FeruzTopalov/spoke/Enclosure/Enterprise/Enterprise_4.jpg

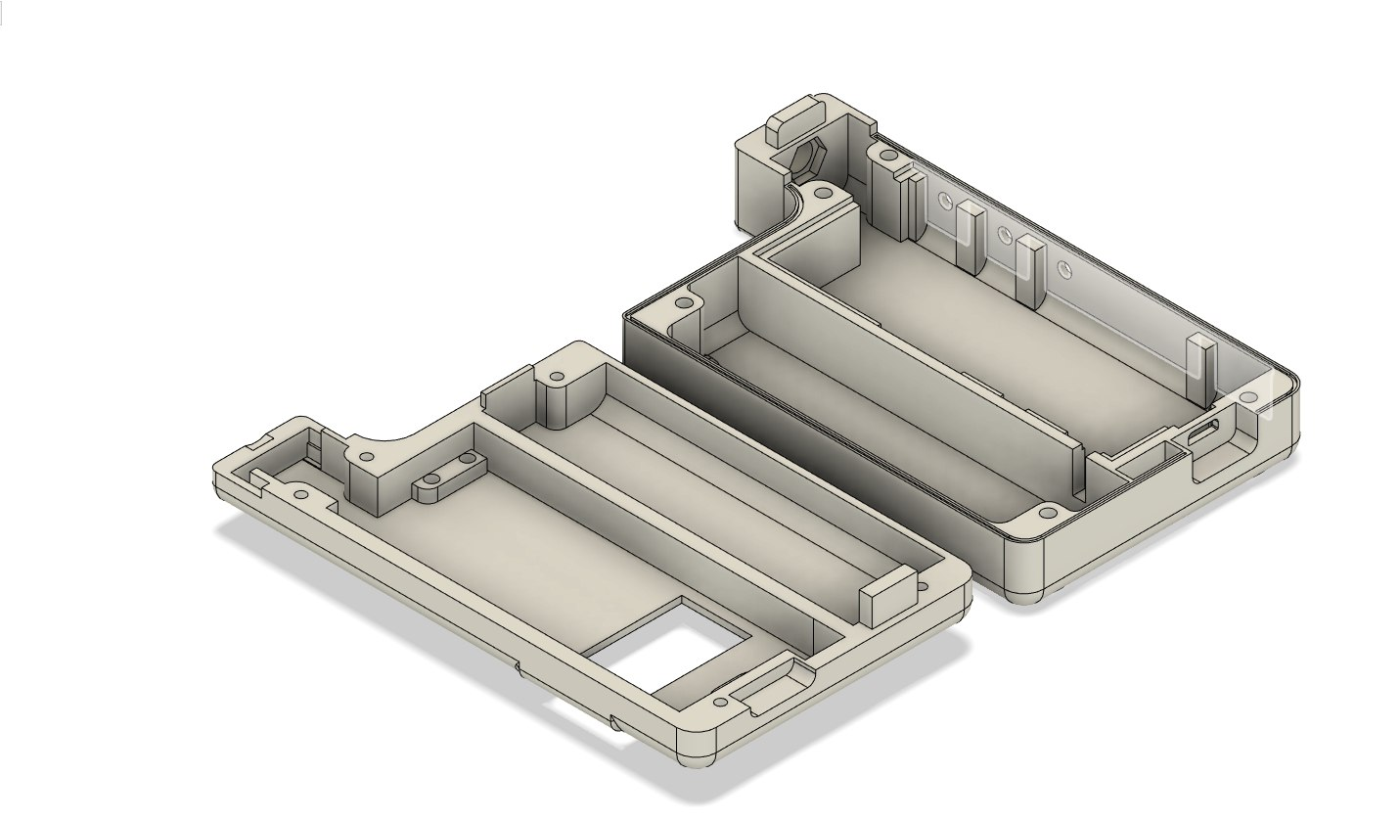
Enclosure/Enterprise/Enterprise_4.jpg
