FeruzTopalov/spoke/Enclosure/Enterprise/Enterprise_real_2.jpg

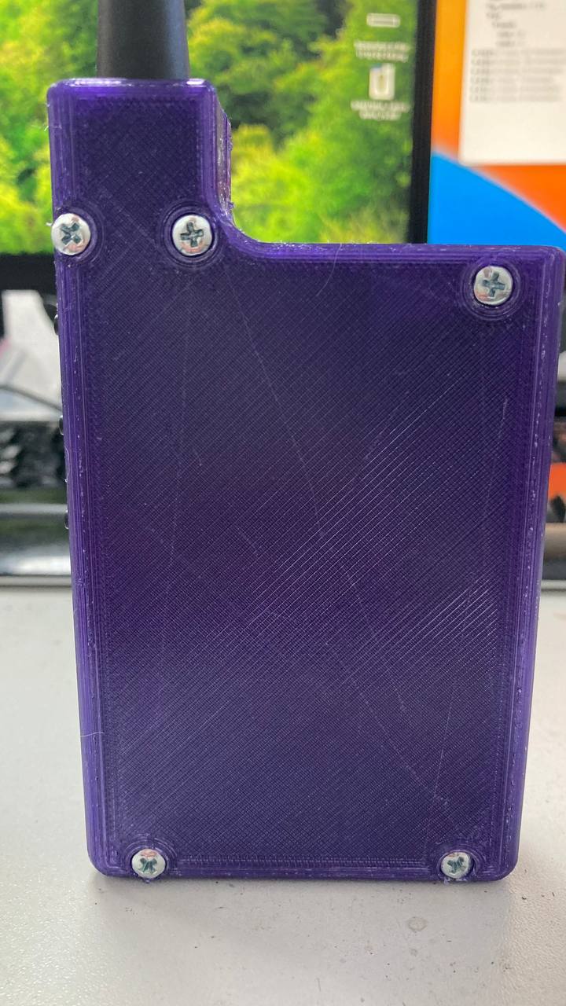
Enclosure/Enterprise/Enterprise_real_2.jpg
