FeruzTopalov/spoke/Enclosure/Enterprise/Enterprise_real_3.jpg

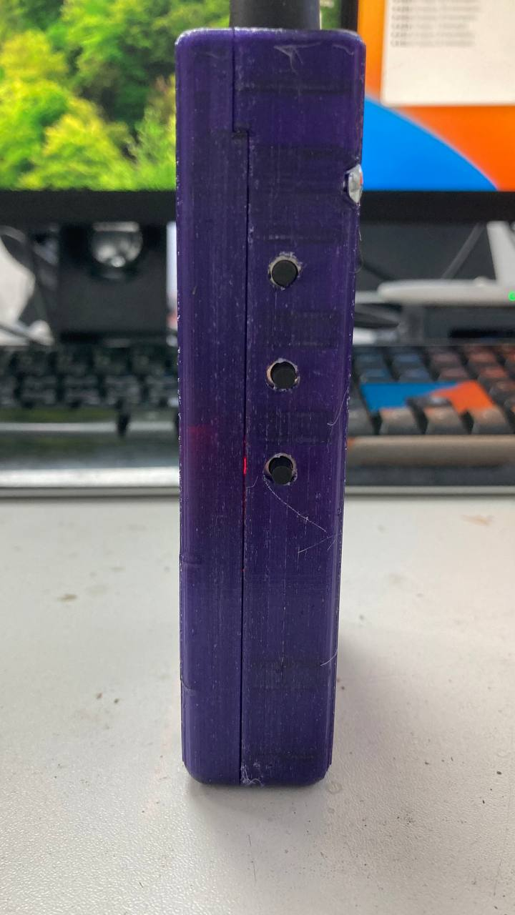
Enclosure/Enterprise/Enterprise_real_3.jpg
