FeruzTopalov/spoke/Enclosure/Pioneer/Pioneer_bot.JPG

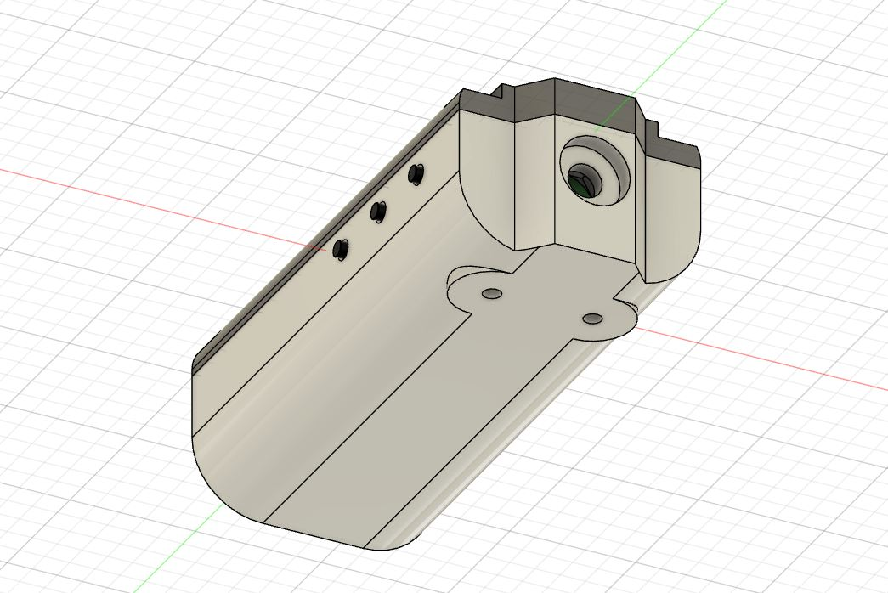
Enclosure/Pioneer/Pioneer_bot.JPG
