FeruzTopalov/spoke/Enclosure/Voyager/Voyager_bot.jpg

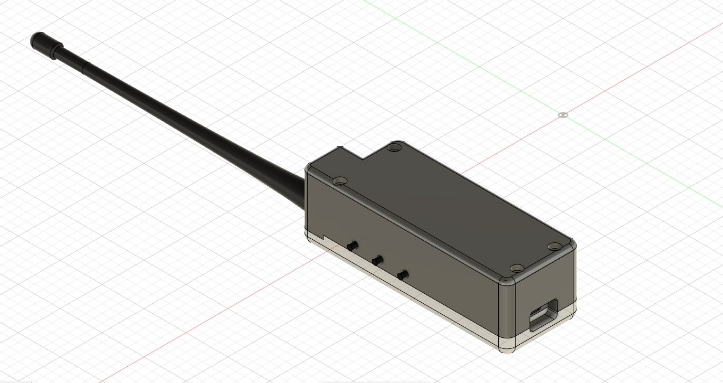
Enclosure/Voyager/Voyager_bot.jpg
