FeruzTopalov/spoke/CubeIDE/Code/inc/lcd_font8x16.h

/*
    SPOKE
    
    file: lcd_font8x16.h
*/



#ifndef LCD_FONT8X16_HEADER
#define LCD_FONT8X16_HEADER



//GLCD FontName : Fixedsys8x16
//GLCD FontSize : 8 x 16
const uint8_t font_8x16[] =
{
	0x00, 0x00, 0xF0, 0x07, 0xF8, 0x0F, 0x08, 0x0B, 0x68, 0x08, 0xF8, 0x0F, 0xF0, 0x07, 0x00, 0x00,   // 0 0   //all symbols from 0x00 to 0x1F are ASCII '0'
	0x00, 0x00, 0xF0, 0x07, 0xF8, 0x0F, 0x08, 0x0B, 0x68, 0x08, 0xF8, 0x0F, 0xF0, 0x07, 0x00, 0x00,   // 0 1
	0x00, 0x00, 0xF0, 0x07, 0xF8, 0x0F, 0x08, 0x0B, 0x68, 0x08, 0xF8, 0x0F, 0xF0, 0x07, 0x00, 0x00,   // 0 2
	0x00, 0x00, 0xF0, 0x07, 0xF8, 0x0F, 0x08, 0x0B, 0x68, 0x08, 0xF8, 0x0F, 0xF0, 0x07, 0x00, 0x00,   // 0 3
	0x00, 0x00, 0xF0, 0x07, 0xF8, 0x0F, 0x08, 0x0B, 0x68, 0x08, 0xF8, 0x0F, 0xF0, 0x07, 0x00, 0x00,   // 0 4
	0x00, 0x00, 0xF0, 0x07, 0xF8, 0x0F, 0x08, 0x0B, 0x68, 0x08, 0xF8, 0x0F, 0xF0, 0x07, 0x00, 0x00,   // 0 5
	0x00, 0x00, 0xF0, 0x07, 0xF8, 0x0F, 0x08, 0x0B, 0x68, 0x08, 0xF8, 0x0F, 0xF0, 0x07, 0x00, 0x00,   // 0 6
	0x00, 0x00, 0xF0, 0x07, 0xF8, 0x0F, 0x08, 0x0B, 0x68, 0x08, 0xF8, 0x0F, 0xF0, 0x07, 0x00, 0x00,   // 0 7
	0x00, 0x00, 0xF0, 0x07, 0xF8, 0x0F, 0x08, 0x0B, 0x68, 0x08, 0xF8, 0x0F, 0xF0, 0x07, 0x00, 0x00,   // 0 8
	0x00, 0x00, 0xF0, 0x07, 0xF8, 0x0F, 0x08, 0x0B, 0x68, 0x08, 0xF8, 0x0F, 0xF0, 0x07, 0x00, 0x00,   // 0 9
	0x00, 0x00, 0xF0, 0x07, 0xF8, 0x0F, 0x08, 0x0B, 0x68, 0x08, 0xF8, 0x0F, 0xF0, 0x07, 0x00, 0x00,   // 0 10
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
    0x00, 0x07, 0x00, 0x03, 0x00, 0x03, 0x00, 0xFF, 0x00, 0xFF, 0x00, 0x03, 0x00, 0x03, 0x00, 0x07   // Code for char 'T' true north
};



#endif /*LCD_FONT8X16_HEADER*/
