FeruzTopalov/spoke/CubeIDE/Code/inc/lcd_font6x8.h

/*
    SPOKE

    file: lcd_font6x8.h
*/

#ifndef LCD_FONT6X8_HEADER
#define LCD_FONT6X8_HEADER



const uint8_t font_6x8[][5] =
{
   { 0x00, 0x00, 0x00, 0x00, 0x00 },   //   0x20  32
   { 0x00, 0x00, 0x5F, 0x00, 0x00 },   // ! 0x21  33
   { 0x00, 0x07, 0x00, 0x07, 0x00 },   // " 0x22  34
   { 0x14, 0x7F, 0x14, 0x7F, 0x14 },   // # 0x23  35
   { 0x24, 0x2A, 0x7F, 0x2A, 0x12 },   // $ 0x24  36
   { 0x4C, 0x2C, 0x10, 0x68, 0x64 },   // % 0x25  37
   { 0x36, 0x49, 0x55, 0x22, 0x50 },   // & 0x26  38
   { 0x00, 0x05, 0x03, 0x00, 0x00 },   // ' 0x27  39
   { 0x00, 0x1C, 0x22, 0x41, 0x00 },   // ( 0x28  40
   { 0x00, 0x41, 0x22, 0x1C, 0x00 },   // ) 0x29  41
   { 0x14, 0x08, 0x3E, 0x08, 0x14 },   // * 0x2A  42
   { 0x08, 0x08, 0x3E, 0x08, 0x08 },   // + 0x2B  43
   { 0x00, 0x00, 0x50, 0x30, 0x00 },   // , 0x2C  44
   { 0x10, 0x10, 0x10, 0x10, 0x10 },   // - 0x2D  45
   { 0x00, 0x60, 0x60, 0x00, 0x00 },   // . 0x2E  46
   { 0x20, 0x10, 0x08, 0x04, 0x02 },   // / 0x2F  47
   { 0x3E, 0x51, 0x49, 0x45, 0x3E },   // 0 0x30  48
   { 0x00, 0x42, 0x7F, 0x40, 0x00 },   // 1 0x31  49
   { 0x42, 0x61, 0x51, 0x49, 0x46 },   // 2 0x32  50
   { 0x21, 0x41, 0x45, 0x4B, 0x31 },   // 3 0x33  51
   { 0x18, 0x14, 0x12, 0x7F, 0x10 },   // 4 0x34  52
   { 0x27, 0x45, 0x45, 0x45, 0x39 },   // 5 0x35  53
   { 0x3C, 0x4A, 0x49, 0x49, 0x30 },   // 6 0x36  54
   { 0x01, 0x71, 0x09, 0x05, 0x03 },   // 7 0x37  55
   { 0x36, 0x49, 0x49, 0x49, 0x36 },   // 8 0x38  56
   { 0x06, 0x49, 0x49, 0x29, 0x1E },   // 9 0x39  57
   { 0x00, 0x36, 0x36, 0x00, 0x00 },   // : 0x3A  58
   { 0x00, 0x56, 0x36, 0x00, 0x00 },   // ; 0x3B  59
   { 0x08, 0x14, 0x22, 0x41, 0x00 },   // < 0x3C  60
   { 0x14, 0x14, 0x14, 0x14, 0x14 },   // = 0x3D  61
   { 0x00, 0x41, 0x22, 0x14, 0x08 },   // > 0x3E  62
   { 0x02, 0x01, 0x51, 0x09, 0x06 },   // ? 0x3F  63
   { 0x32, 0x49, 0x79, 0x41, 0x3E },   // @ 0x40  64
   { 0x7E, 0x11, 0x11, 0x11, 0x7E },   // A 0x41  65
   { 0x7F, 0x49, 0x49, 0x49, 0x36 },   // B 0x42  66
   { 0x3E, 0x41, 0x41, 0x41, 0x22 },   // C 0x43  67
   { 0x7F, 0x41, 0x41, 0x22, 0x1C },   // D 0x44  68
   { 0x7F, 0x49, 0x49, 0x49, 0x41 },   // E 0x45  69
   { 0x7F, 0x09, 0x09, 0x09, 0x01 },   // F 0x46  70
   { 0x3E, 0x41, 0x49, 0x49, 0x7A },   // G 0x47  71
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
};



#endif /* LCD_FONT6X8_HEADER */
