FeruzTopalov/spoke/CubeIDE/Code/inc/lrns.h

/*
    SPOKE

    file: lrns.h
*/



#ifndef LRNS_HEADER
#define LRNS_HEADER



#define DEVICES_ON_AIR_MAX	(5)												//max number of devices on air (real Spoke devices)
#define MEMORY_POINTS_TOT	(4)												//total number of memory points
#define NAV_OBJECTS_MAX		(DEVICES_ON_AIR_MAX + MEMORY_POINTS_TOT)         //max number of devices including real Spoke devices and memory points

#define DEVICE_NUMBER_FIRST (1)
#define DEVICE_NUMBER_LAST  (DEVICES_ON_AIR_MAX)

#define MEMORY_POINT_FIRST	(DEVICES_ON_AIR_MAX + 1)
#define MEMORY_POINT_LAST	(MEMORY_POINT_FIRST + MEMORY_POINTS_TOT - 1)

#define NAV_OBJECT_NULL 	(0)
#define NAV_OBJECT_FIRST 	(1)
#define NAV_OBJECT_LAST  	(NAV_OBJECTS_MAX)



#define ACC_MOVEMENT_NOT_DETECTED 	(0)
#define ACC_MOVEMENT_DETECTED 		(1)



#define LRNS_RADIO_ACTION_TX				(1)
#define LRNS_RADIO_ACTION_RX				(2)
#define LRNS_RADIO_ACTION_RX_ACTIVE_DEV		(3)



extern const double deg_to_rad;       //deg to rad multiplyer



void init_lrns(void);
uint8_t get_lrns_protocol_radio_action(void);
void fill_air_packet(uint32_t current_uptime);
uint8_t parse_air_packet(uint32_t current_uptime);
void process_all_devices(void);
void calc_relative_position(uint8_t another_device);
void calc_timeout(uint32_t current_uptime);
void calc_fence(void);
uint8_t check_any_alarm_fence_timeout(void);
void clear_beep_for_active_dev(uint8_t active_device);
void toggle_my_alarm(void);
void enable_my_alarm(void);
uint8_t get_my_alarm_status(void);
void set_lowbat_flag(uint8_t value);
void set_acc_movement_flag(uint8_t value);
struct devices_struct **get_devices(void);



//Struct with all devices info
struct devices_struct
{
	//COMMON
    char device_id;  				//a device id, single ASCII symbol
	uint8_t exist_flag;             //does a device exist?
    uint8_t memory_point_flag;		//is this device a memory point?
	uint8_t alarm_flag;				//is alarm reported by a device?
	uint8_t alarm_flag_for_beep;	//for beep clear
	uint8_t fence_flag;				//is a predefined fence distance reached?
	uint8_t fence_flag_for_beep;	//for beep clear
	uint8_t beacon_flag;			//is device a beacon?
	uint8_t lowbat_flag;			//did the device transmit low battery flag?
	uint8_t acc_movement_flag;		//flag if accelerometer detected movement in the recent update interval
	uint8_t pdop_good_flag;			//GPS PDOP quality flag
	int8_t lora_snr;				//SNR of the last received packet

    //TIME
    uint32_t timestamp;					//time stamp in seconds when the last activity was detected
    uint32_t timeout;					//timeout in seconds since last activity (RX of coordinates)
    uint8_t timeout_flag;				//set when predefined timeout occurs
    uint8_t timeout_flag_for_beep;		//for beep clear
    uint8_t link_status_flag;			//link status symbol for navigation screen

    //DATE (only for memory points)
    uint8_t save_day;
	uint8_t save_month;
	uint8_t save_year;

    //ABSOLUTE COORDINATES
    union
    {
        float as_float;             //latitude in decimal degrees (-90...+90)
        uint8_t as_array[4];
    } latitude;

    union
    {
        float as_float;             //longitude in decimal degrees (-180...+180)
        uint8_t as_array[4];
    } longitude;

    union
    {
        int16_t as_integer;         //altitude in meters, signed
        uint8_t as_array[2];
    } altitude;


    //RELATIVE COORDINATES
    uint32_t distance;          //distance in meters to a device
    uint16_t heading_deg;       //heading to a device, degrees
    float heading_rad;			//heading to a device, radians
    int16_t delta_altitude;		//delta altitude
};



#endif /*LRNS_HEADER*/
