FeruzTopalov/spoke/CubeIDE/Code/inc/lcd.h

/*
    SPOKE
    
    file: lcd.h
*/



#ifndef LCD_HEADER
#define LCD_HEADER



#define LCD_DISPLAY_ON	(1)
#define LCD_DISPLAY_OFF	(0)



#define LCD_ROWS_8X16       	(4)
#define LCD_COLS_8X16     		(16)

#define LCD_ROWS_6X8       		(8)
#define LCD_COLS_6X8     		(21)



#define SYMB16_HOME			('=')

#define SYMB8_DEGREE        ('\x80')
#define SYMB8_BAT_TAIL    	('\x81')
#define SYMB8_BAT_MID    	('\x82')
#define SYMB8_BAT_HEAD    	('\x83')
#define SYMB8_TIMEOUT       ('\x84')
#define SYMB8_FENCE       	('\x85')
#define SYMB8_ALARM       	('\x86')
#define SYMB8_LINK_OK    	('\x87')	//check mark
#define SYMB8_LINK_LOST    	('\x88')	//question mark
#define SYMB8_MAG_NORTH    	('\x89')
#define SYMB8_TRUE_NORTH  	('\x8A')



#define LCD_SIZE_BYTES    	(1024)
#define LCD_SIZE_X        	(128)
#define LCD_SIZE_Y        	(64)
#define LCD_CENTR_X 		(64)
#define LCD_CENTR_Y 		(32)



void lcd_init(void);
void lcd_send_command(uint8_t command);
void lcd_display_on(void);
void lcd_display_off(void);
void lcd_display_off_request(void);
uint8_t lcd_get_display_status(void);
void lcd_toggle_backlight_opt(uint8_t bl_option);
void reset_backlight_counter(void);
void decrement_backlight_counter(void);
void lcd_fill(void);
void lcd_clear(void);
void lcd_pixel(uint8_t x, uint8_t y, int8_t action);
void lcd_set_pixel(uint8_t x, uint8_t y);
void lcd_set_pixel_plot(uint8_t x, uint8_t y);
void lcd_pos_6x8(uint8_t row, uint8_t col);
void lcd_pos_8x16(uint8_t row, uint8_t col);
void lcd_char_6x8(char chr);
void lcd_char_8x16(char chr);
void lcd_char_8x16_overlay(char chr);
void lcd_char_16x16(char chr);
void lcd_char_8x16_pos(uint8_t row, uint8_t col, char chr);
void lcd_char_8x16_overlay_pos(uint8_t row, uint8_t col, char chr);
void lcd_char_16x16_pos(uint8_t row, uint8_t col, char chr);
void lcd_print_small(uint8_t row, uint8_t col, char *p_str);
void lcd_print_small_next(char *p_str);
void lcd_print(uint8_t row, uint8_t col, char *p_str);
void lcd_print_only(uint8_t row, uint8_t col, char *p_str);
void lcd_print_large(uint8_t row, uint8_t col, char *p_str);
void lcd_print_next(char *p_str);
void lcd_print_viceversa(uint8_t row, uint8_t col, char *p_str);
void lcd_print_next_viceversa(char *p_str);
void lcd_print_large_viceversa(uint8_t row, uint8_t col, char *p_str);
void lcd_bitmap(const uint8_t arr[]);
void lcd_update(void);
void lcd_continue_update(void);
void lcd_print_byte(uint8_t row, uint8_t col, uint8_t byte);
void lcd_byte2buf(uint16_t pos, uint8_t byte);
void lcd_draw_line(int8_t x1, int8_t y1, int8_t x2, int8_t y2);
void lcd_draw_dot(int8_t x0, int8_t y0);
void lcd_draw_big_dot(int8_t x0, int8_t y0);
uint8_t *get_lcd_buffer(void);
uint8_t get_lcd_busy(void);



#endif /*LCD_HEADER*/
