FeruzTopalov/spoke/CubeIDE/Code/inc/lcd_bitmaps.h

/*
    SPOKE
    
    file: lcd_bitmaps.h
*/



#ifndef LCD_BITMAPS_HEADER
#define LCD_BITMAPS_HEADER



extern const uint8_t startup_screen[1024];
extern const uint8_t spoke_blank[1024];



#endif /*LCD_BITMAPS_HEADER*/
