FeruzTopalov/spoke/CubeIDE/Code/inc/spi.h

/*
    SPOKE
    
    file: spi.h
*/



#ifndef SPI_HEADER
#define SPI_HEADER



void spi_init(void);

void spi1_init(void);
void spi1_clock_disable(void);
void spi1_clock_enable(void);
uint8_t spi1_trx(uint8_t send_data);

void spi2_dma_init(uint8_t buffer[], uint32_t buffer_len);
void spi2_dma_start(uint8_t buffer[], uint32_t buffer_len);
void spi2_dma_stop(void);
void spi2_clock_disable(void);
void spi2_clock_enable(void);
void spi2_tx(uint8_t send_data);



#endif /*SPI_HEADER*/
