FeruzTopalov/spoke/CubeIDE/Code/inc/points.h

/*
    SPOKE

    file: points.h
*/



#ifndef POINTS_HEADER
#define POINTS_HEADER

void init_memory_points(void);
void load_memory_points(void);
void store_memory_points(void);
char *get_memory_point_name(uint8_t point_number);

#endif /*POINTS_HEADER*/
